bcorner13/LeftDoorPocket/images/Screenshot 2026-03-26 at 9.16.25 PM.png

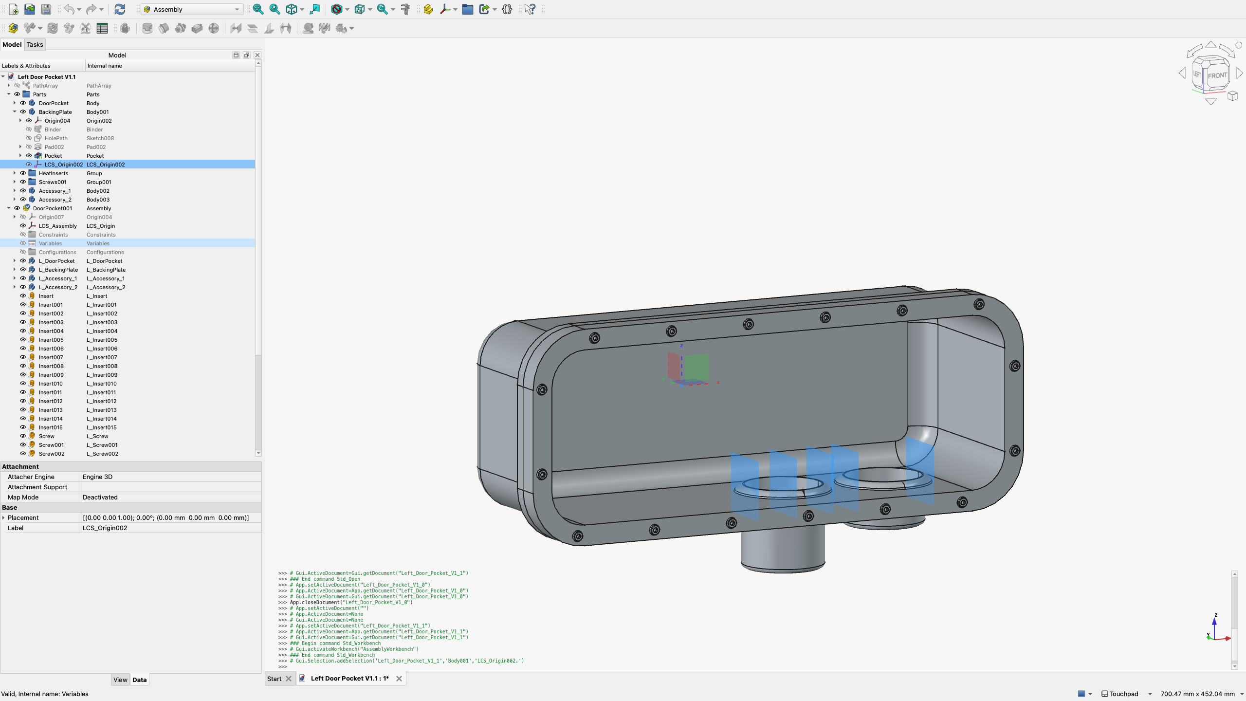
images/Screenshot 2026-03-26 at 9.16.25 PM.png
