bcorner13/LeftDoorPocket/images/Screenshot 2026-03-26 at 10.08.45 PM.png

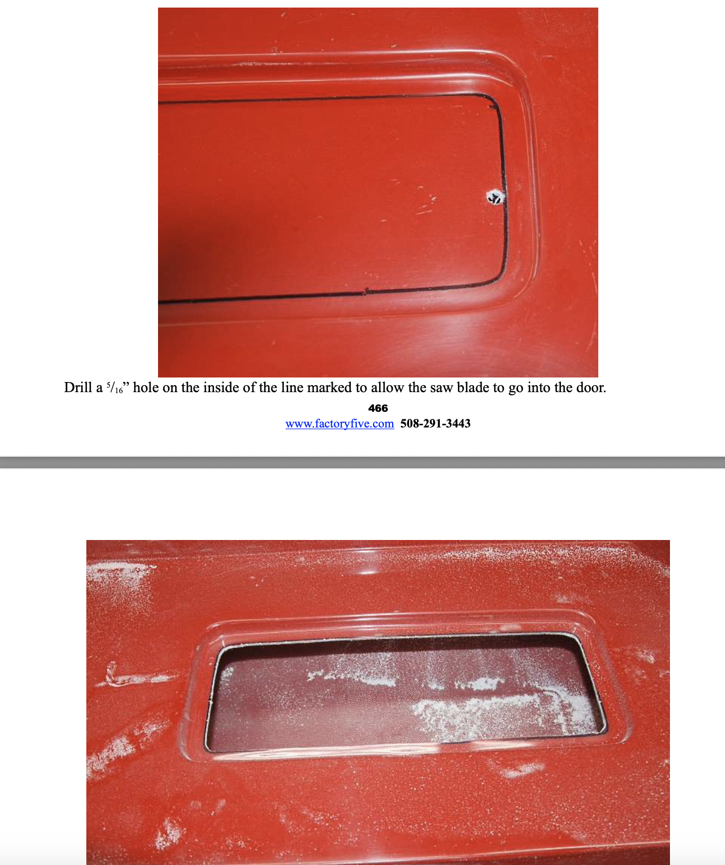
images/Screenshot 2026-03-26 at 10.08.45 PM.png
