bcorner13/LeftDoorPocket/images/Screenshot 2026-03-26 at 10.26.11 PM.png

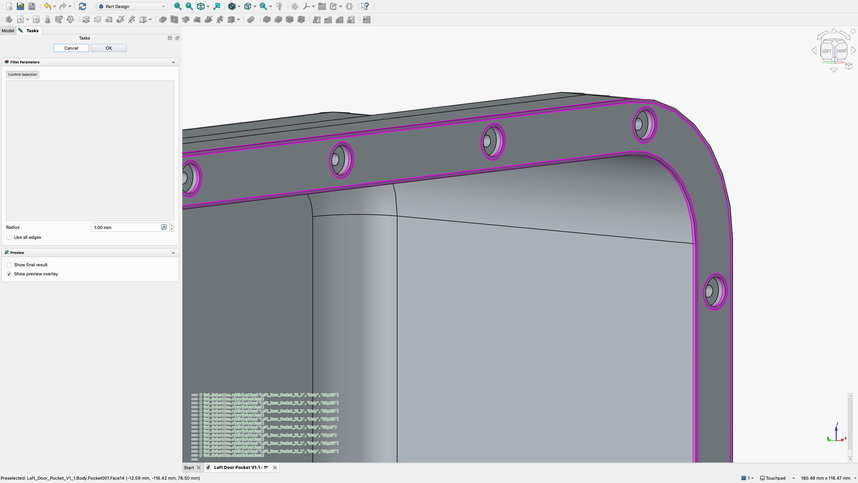
images/Screenshot 2026-03-26 at 10.26.11 PM.png
